Maddca/Short-Wave-Software-Defined-Receiver/Images/SDR BandPass Filter LTSpice.png

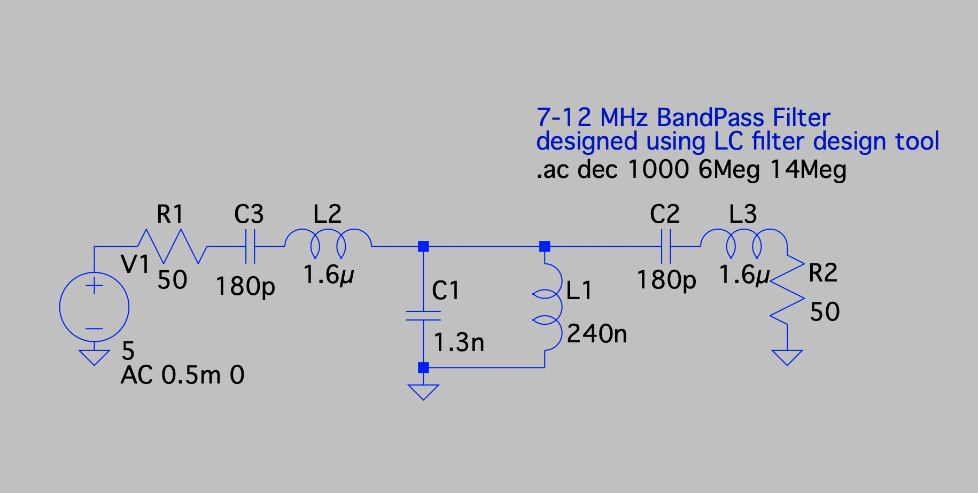
Images/SDR BandPass Filter LTSpice.png
