Maddca/Short-Wave-Software-Defined-Receiver/Images/SDR Block Diagram.png

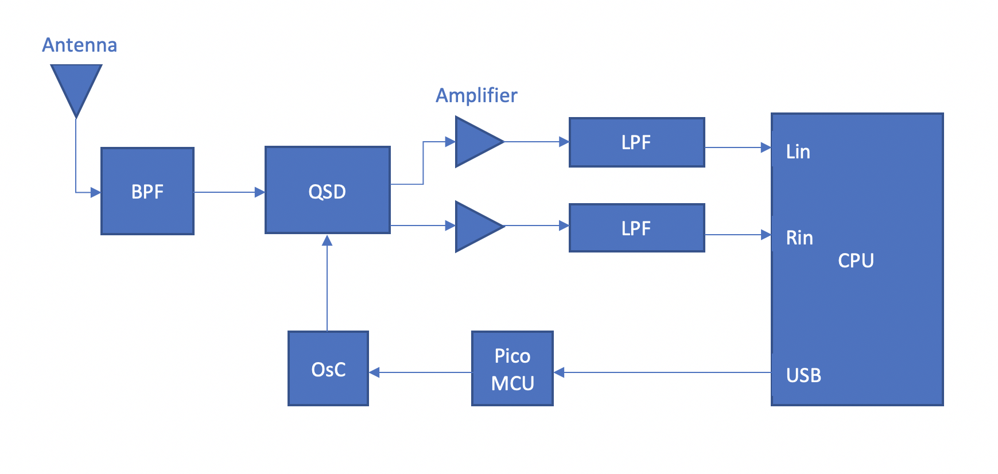
Images/SDR Block Diagram.png
