Maddca/Short-Wave-Software-Defined-Receiver/Images/SDR MFLPFA LTSpice.png

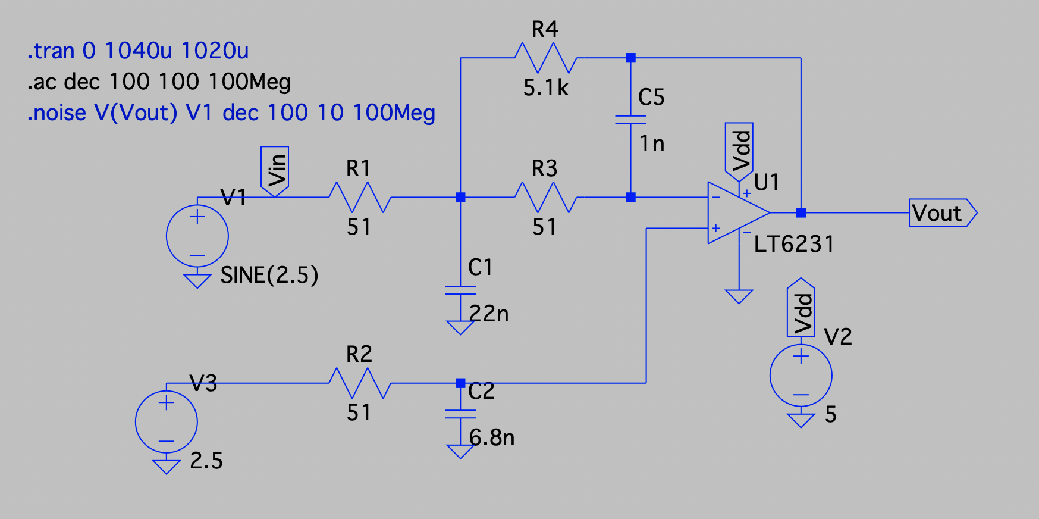
Images/SDR MFLPFA LTSpice.png
