Maddca/Short-Wave-Software-Defined-Receiver/Images/SDR Oscillator.png

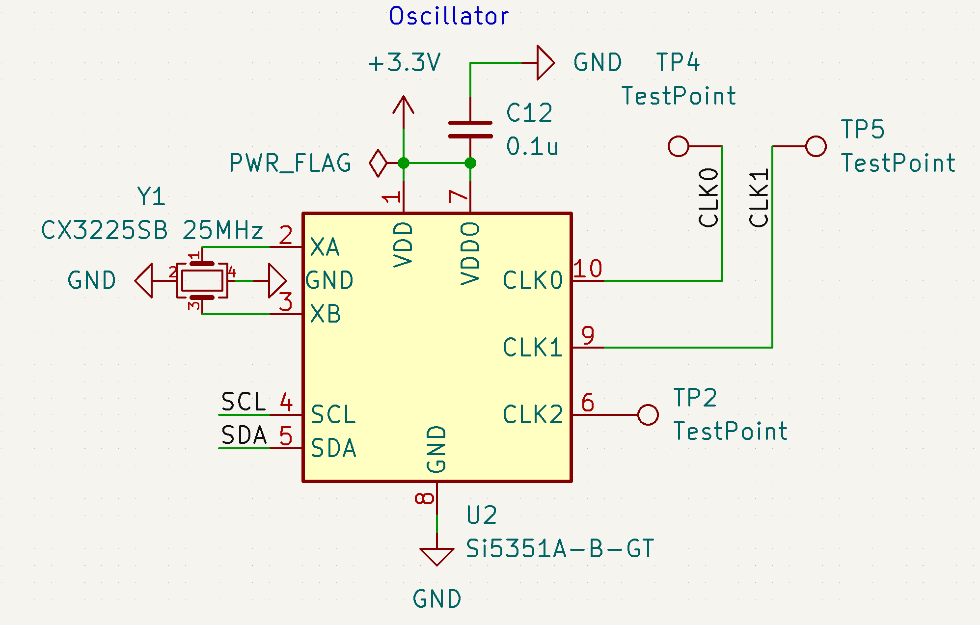
Images/SDR Oscillator.png
