Maddca/Short-Wave-Software-Defined-Receiver/Images/SDR Raspberry Pi Pico.png

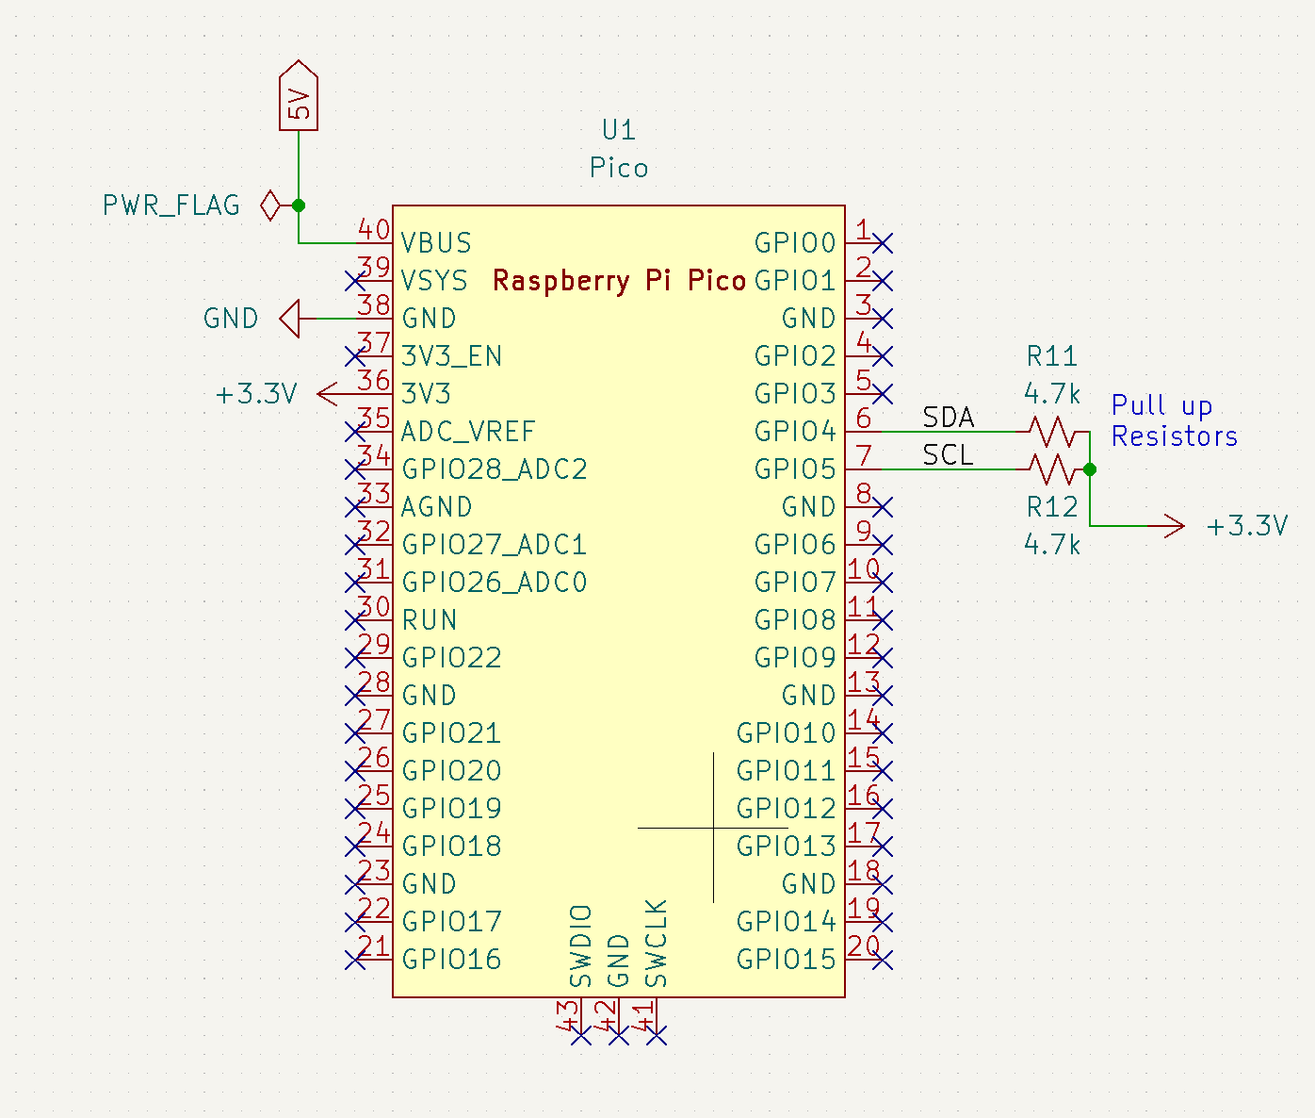
Images/SDR Raspberry Pi Pico.png
