Maddca/Short-Wave-Software-Defined-Receiver/Multiple feedback low pass amplifier.asc

C1: cap; 22n
C2: cap; 7.5n
C5: cap; 14p
R1: res; 51
R2: res; 51
R3: res; 160
R4: res; 51k
U1: LT6231
V2: voltage; 5
Named nets: Output1, Vdd, 0
.tran 0 1040u 1020u
.ac dec 10 6Meg 14Meg
