Maddca/Short-Wave-Software-Defined-Receiver/Simulations/SDR Bandpass Filter 7-12MHz.asc

C1: cap; 1.3n
C2: cap; 180p
C3: cap; 180p
L1: ind; 240n
L2: ind; 1.6µ
L3: ind; 1.6µ
R1: res; 50
R2: res; 50
V1: voltage; 5; AC 1 0
Named nets: 0
.ac dec 1000 6Meg 14Meg
7-12 MHz BandPass Filter
designed using LC filter design tool
