Maddca/Short-Wave-Software-Defined-Receiver/Simulations/Full SDR Simulation.asc

C1: cap; 14p
C2: cap; 22n
C3: cap; 6.8n
C4: cap; 22n
C5: cap; 6.8n
C6: cap; 1n
C10: cap; 2.2n
C12: cap; 130p
C13: cap; 130p
L1: ind; 180n
L2: ind; 2.7µ
L3: ind; 2.7µ
R1: res; 5.1
R2: res; 51
R3: res; 51
R4: res; 51
R5: res; 51
R6: res; 51
R7: res; 10000
R8: res; 10000
R9: res; 50
R10: res; 5.1k
R11: res; 5.1k
S1: sw; MYSW
S2: sw; MYSW
S3: sw; MYSW
S4: sw; MYSW
U1: AD8041
U2: AD8041
V1: voltage; PULSE(0 3.3 0 0.001p 0.001p {SwTime} {4*SwTime})
V2: voltage; 5
V3: voltage; PULSE(0 3.3 {3*SwTime} 0.001p 0.001p {SwTime} {4*SwTime})
V4: voltage; PULSE(0 3.3 {SwTime} 0.001p 0.001p {SwTime} {4*SwTime})
V5: voltage; PULSE(0 3.3 {2*SwTime} 0.001p 0.001p {SwTime} {4*SwTime})
V6: voltage; SINE(0 1 {RF_freq})
Named nets: 0, Output1, Output2, Vdd, 0deg, 90deg, 180deg, 270deg, 00, 01, 10, 11
.tran 0 500u
.ac dec 10 6Meg 14Meg
.model SW SW (Ron=0.1 Roff=1e9 Vt=0.1 Vh=0.0)
.model MYSW SW(Vt=0.9 Vh=0 Ron=1 Roff=100G)
.param RF_freq=10Meg LO_freq={RF_freq - Audio_freq} LO_period={1/LO_freq} SwTime={LO_period/4}
;.step oct param Audio_freq 1000 10000 1
.param Audio_freq = 1000
